BCN3D/Flowy-Oven/img/IMG_20151116_104900.jpg

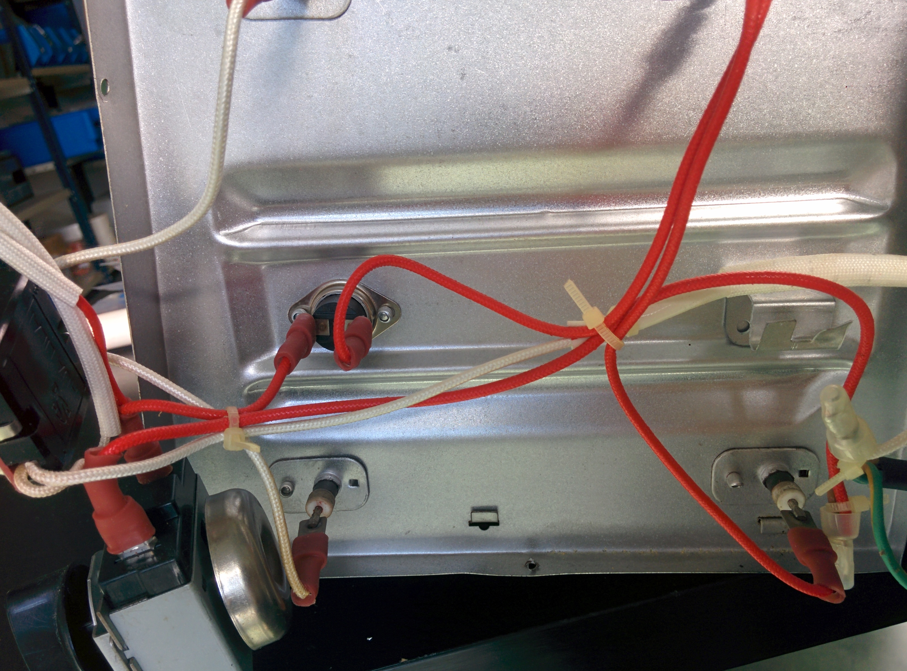
img/IMG_20151116_104900.jpg
