BCN3D/Flowy-Oven/img/IMG_20151126_135641.jpg

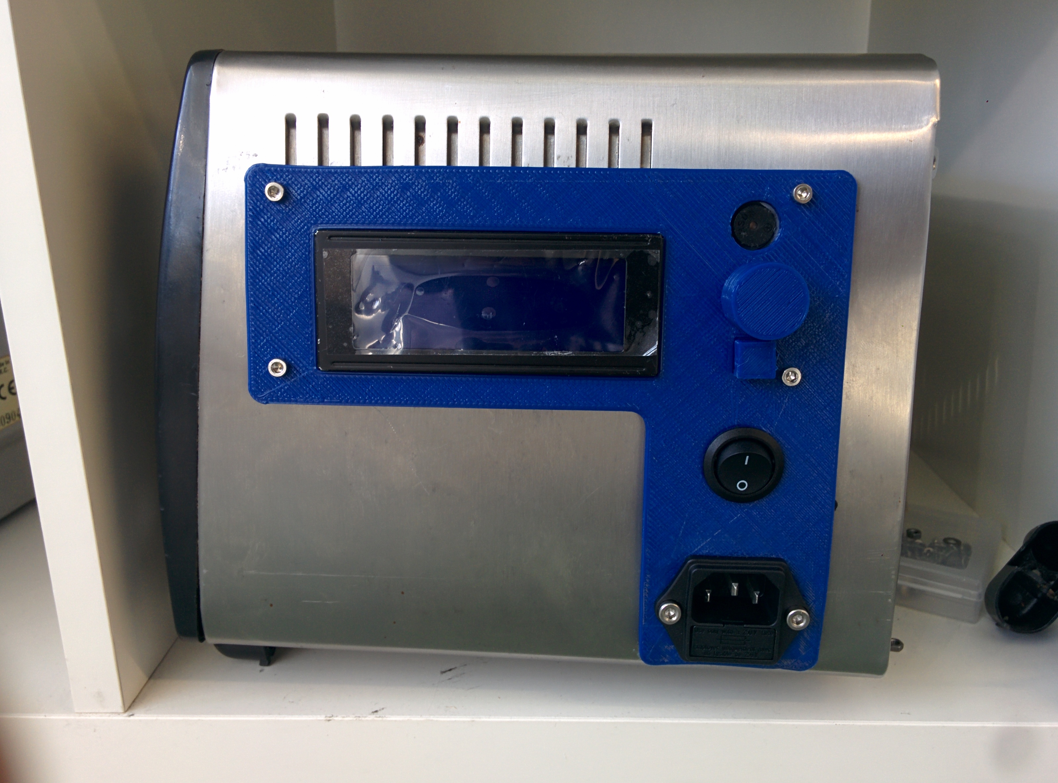
img/IMG_20151126_135641.jpg
