BCN3D/Flowy-Oven/img/IMG_20151209_114248.jpg

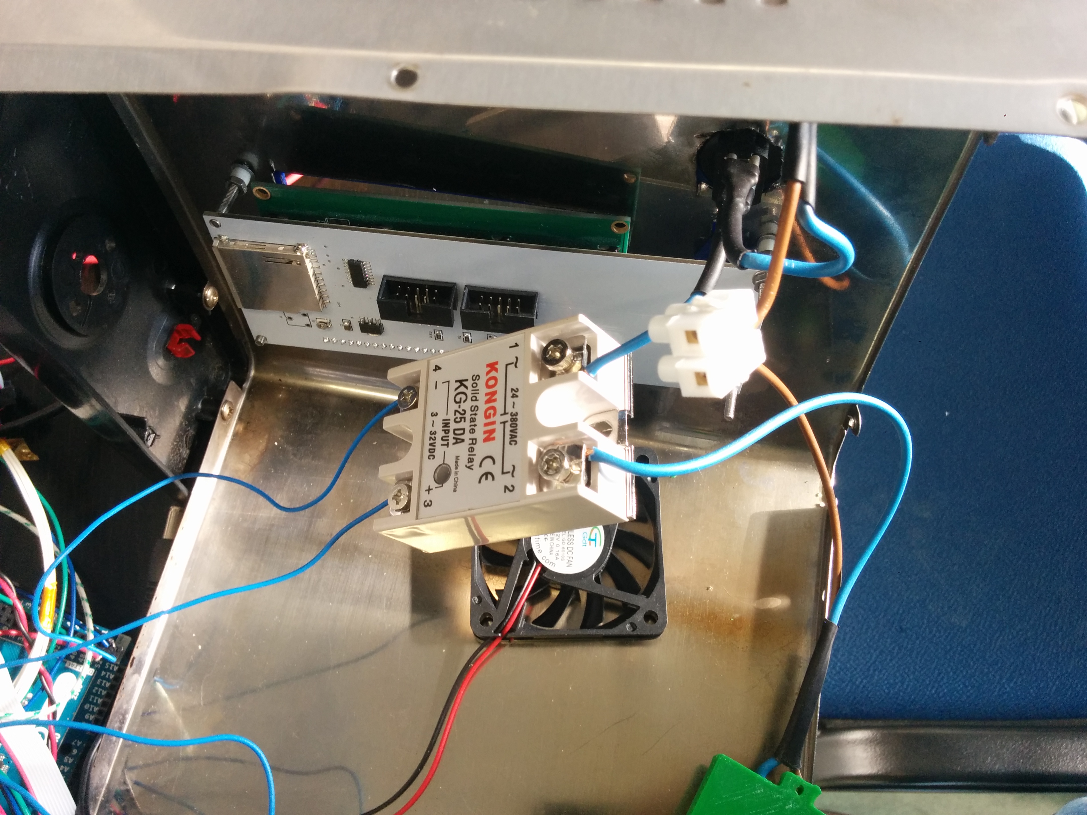
img/IMG_20151209_114248.jpg
