BCN3D/Flowy-Oven/img/IMG_20151209_114259.jpg

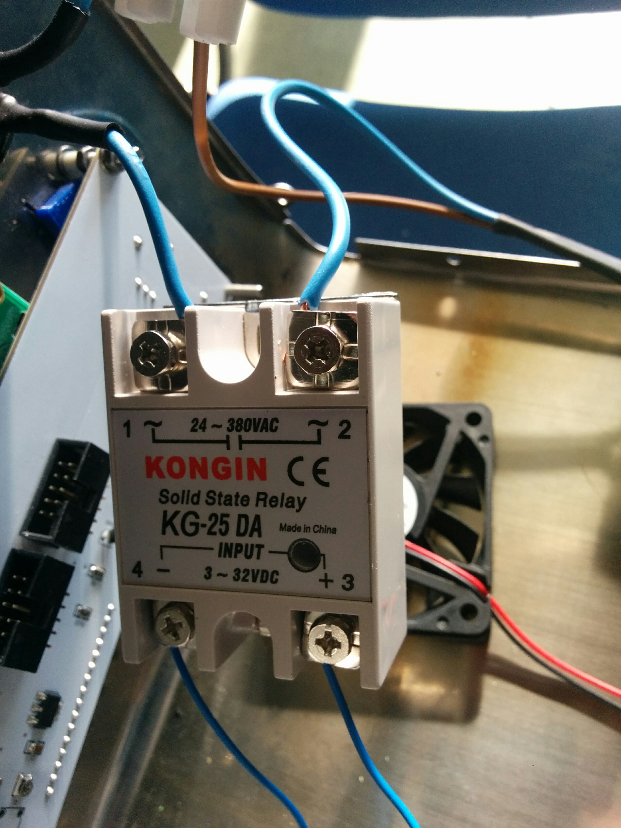
img/IMG_20151209_114259.jpg
