BCN3D/Flowy-Oven/img/IMG_20151211_125600.jpg

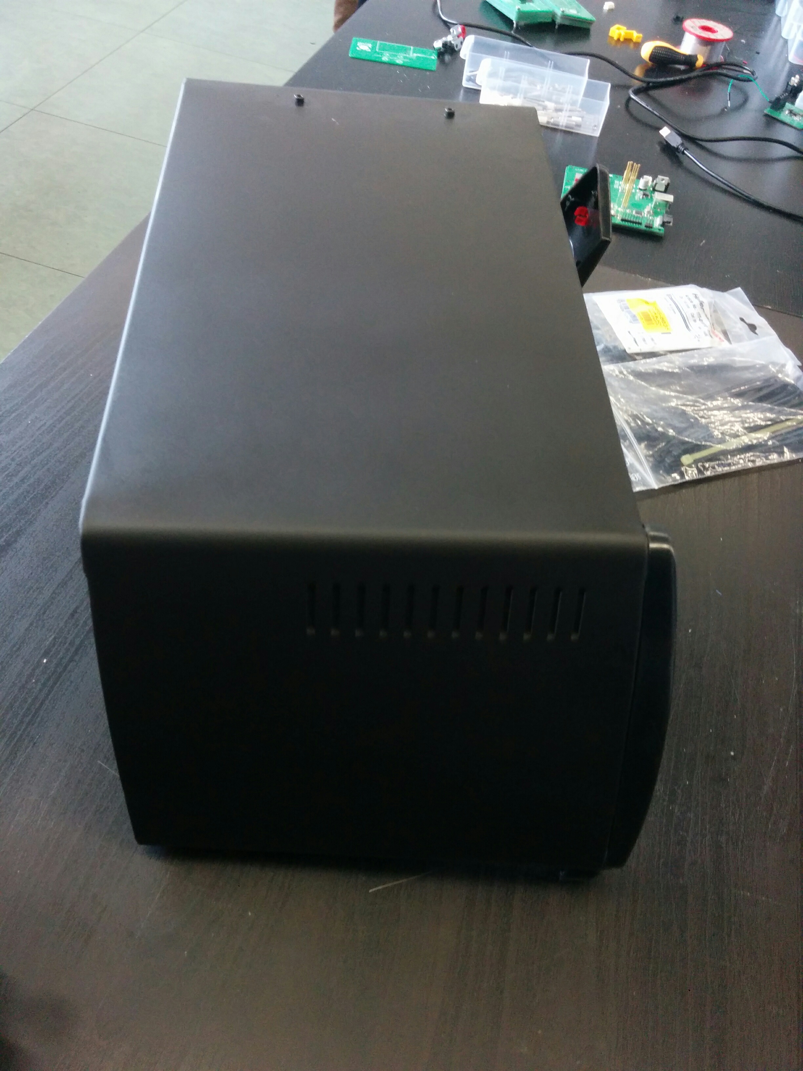
img/IMG_20151211_125600.jpg
