BCN3D/Flowy-Oven/img/IMG_20160113_123552.jpg

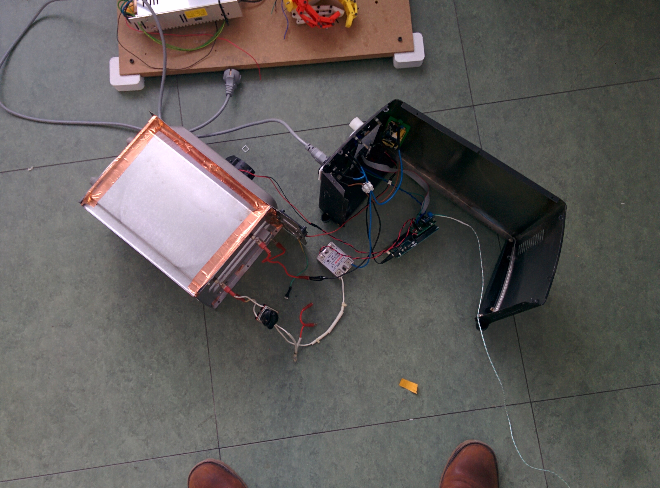
img/IMG_20160113_123552.jpg
